Protocentral/Protocentral_ADS1220/src/Protocentral_ADS1220.h

//////////////////////////////////////////////////////////////////////////////////////////
//
//    Arduino library for the ADS1220 24-bit ADC breakout board
//
//    Author: Ashwin Whitchurch
//    Copyright (c) 2018 ProtoCentral
//
//    Based on original code from Texas Instruments
//
//    This software is licensed under the MIT License(http://opensource.org/licenses/MIT).
//
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
//   For information on how to use, visit https://github.com/Protocentral/Protocentral_ADS1220/
//
/////////////////////////////////////////////////////////////////////////////////////////

#pragma once

#include "Arduino.h"

#include <SPI.h>

//ADS1220 SPI commands
#define SPI_MASTER_DUMMY    0xFF
#define RESET               0x06   //Send the RESET command (06h) to make sure the ADS1220 is properly reset after power-up
#define START               0x08    //Send the START/SYNC command (08h) to start converting in continuous conversion mode
#define WREG  0x40
#define RREG  0x20

//Config registers
#define CONFIG_REG0_ADDRESS 0x00
#define CONFIG_REG1_ADDRESS 0x01
#define CONFIG_REG2_ADDRESS 0x02
#define CONFIG_REG3_ADDRESS 0x03

#define REG_CONFIG3_IDAC1routing_MASK    0xE0
#define REG_CONFIG3_IDAC2routing_MASK    0x1C
#define REG_CONFIG2_VREF_MASK            0xC0
#define REG_CONFIG2_FIR_MASK             0x30
#define REG_CONFIG2_IDACcurrent_MASK     0x07
#define REG_CONFIG1_MODE_MASK            0x18
#define REG_CONFIG1_DR_MASK       0xE0
#define REG_CONFIG0_PGA_GAIN_MASK 0x0E
#define REG_CONFIG0_MUX_MASK      0xF0

#define IDAC1_disable     0x00  
#define IDAC1_AIN0        0x20  
#define IDAC1_AIN1        0x40  
#define IDAC1_AIN2        0x60  
#define IDAC1_AIN3        0x80  
#define IDAC1_REFP0       0xA0  
#define IDAC1_REFN0       0xC0  
#define IDAC1_reserved    0xE0  

#define IDAC2_disable     0x00  
#define IDAC2_AIN0        0x04  
#define IDAC2_AIN1        0x08  
#define IDAC2_AIN2        0x0C  
#define IDAC2_AIN3        0x10  
#define IDAC2_REFP0       0x14  
#define IDAC2_REFN0       0x18  
#define IDAC2_reserved    0x1C  

#define IDAC_OFF     0x00  
#define IDAC_10      0x01  
#define IDAC_50      0x02  
#define IDAC_100     0x03  
#define IDAC_250     0x04  
#define IDAC_500     0x05  
#define IDAC_1000    0x06  
#define IDAC_1500    0x07  

#define FIR_OFF      0x00  
#define FIR_5060     0x10  
#define FIR_50Hz     0x20  
#define FIR_60Hz     0x30  

#define VREF_2048       0x00  
#define VREF_REFP0      0x40  
#define VREF_AIN0       0x80  
#define VREF_ANALOG     0xC0  

#define MODE_NORMAL     0x00  
#define MODE_DUTYCYCLE  0x08  
#define MODE_TURBO      0x10  
#define MODE_RESERVED   0x18  

#define DR_20SPS    0x00
#define DR_45SPS    0x20
#define DR_90SPS    0x40
#define DR_175SPS   0x60
#define DR_330SPS   0x80
#define DR_600SPS   0xA0
#define DR_1000SPS  0xC0

#define PGA_GAIN_1   0x00
#define PGA_GAIN_2   0x02
#define PGA_GAIN_4   0x04
#define PGA_GAIN_8   0x06
#define PGA_GAIN_16  0x08
#define PGA_GAIN_32  0x0A
#define PGA_GAIN_64  0x0C
#define PGA_GAIN_128 0x0E

#define MUX_AIN0_AIN1   0x00
#define MUX_AIN0_AIN2   0x10
#define MUX_AIN0_AIN3   0x20
#define MUX_AIN1_AIN2   0x30
#define MUX_AIN1_AIN3   0x40
#define MUX_AIN2_AIN3   0x50
#define MUX_AIN1_AIN0   0x60
#define MUX_AIN3_AIN2   0x70
#define MUX_AIN0_AVSS   0x80
#define MUX_AIN1_AVSS   0x90
#define MUX_AIN2_AVSS   0xA0
#define MUX_AIN3_AVSS   0xB0

#define MUX_SE_CH0      0x80
#define MUX_SE_CH1      0x90
#define MUX_SE_CH2      0xA0
#define MUX_SE_CH3      0xB0


class Protocentral_ADS1220
{
      private:
            uint8_t m_config_reg0;
            uint8_t m_config_reg1;
            uint8_t m_config_reg2;
            uint8_t m_config_reg3;

            uint8_t Config_Reg0;
            uint8_t Config_Reg1;
            uint8_t Config_Reg2;
            uint8_t Config_Reg3;

            uint8_t DataReg[3];

            uint8_t m_drdy_pin=6;
            uint8_t m_cs_pin=7;
      public:
            uint8_t NewDataAvailable;

            Protocentral_ADS1220();
            void begin(uint8_t cs_pin, uint8_t drdy_pin);

            void PrintRegisterValues();

            void Start_Conv(void);
            void ads1220_Reset(void);

            void SPI_Command(unsigned char data_in);
            void writeRegister(uint8_t address, uint8_t value);
            uint8_t readRegister(uint8_t address);
            uint8_t * Read_Data(void);
            int32_t Read_WaitForData();

            bool WaitForData(unsigned int timeout_ms);
            int32_t DataToInt();

            uint8_t * get_config_reg(void);

            // control register 0
            void select_mux_channels(int channels_conf);
            void set_pga_gain(int pgagain);
            void PGA_OFF(void);
            void PGA_ON(void);
            
            // control register 1
            void set_data_rate(int datarate);
            void set_OperationMode(int OPmode);    
            void set_conv_mode_single_shot(void);
            void set_conv_mode_continuous(void);
            void TemperatureSensorMode_enable(void);    
            void TemperatureSensorMode_disable(void);   
            void CurrentSources_ON(void);       
            void CurrentSources_OFF(void);      
            
            // control register 2
            void set_VREF(int vref);             
            void set_FIR_Filter(int filter);     
            void LowSideSwitch_OPEN(void);       
            void LowSideSwitch_CLOSED(void);        
            void set_IDAC_Current(int IDACcurrent);  
            
            // control register 3
            void set_IDAC1_Route(int IDAC1routing);   
            void set_IDAC2_Route(int IDAC2routing);   
            void DRDYmode_default(void);       
            void DRDYmode_DOUT(void);          
            
            // end control register
            int32_t Read_SingleShot_WaitForData(void);
            int32_t Read_SingleShot_SingleEnded_WaitForData(uint8_t channel_no);

            void internal_reference();
            void external_reference();

            int32_t Read_Data_Samples();
};
