Protocentral/Protocentral_ADS1220/examples/Example2-ADS1220-Stream/Example2-ADS1220-Stream.ino

//////////////////////////////////////////////////////////////////////////////////////////
//
//    Demo code for the ADS1220 24-bit ADC breakout board
//
//    Author: Ashwin Whitchurch
//    Copyright (c) 2018 ProtoCentral
//
//    This example gives differential voltage across the AN0 and AN1 pins in mVolts
//
//    Arduino connections:
//
//  |ADS1220 pin label| Pin Function         |Arduino Connection|
//  |-----------------|:--------------------:|-----------------:|
//  | DRDY            | Data ready Output pin|  D02             |
//  | MISO            | Slave Out            |  D12             |
//  | MOSI            | Slave In             |  D11             |
//  | SCLK            | Serial Clock         |  D13             |
//  | CS              | Chip Select          |  D7              |
//  | DVDD            | Digital VDD          |  +5V             |
//  | DGND            | Digital Gnd          |  Gnd             |
//  | AN0-AN3         | Analog Input         |  Analog Input    |
//  | AVDD            | Analog VDD           |  -               |
//  | AGND            | Analog Gnd           |  -               |
//
//    This software is licensed under the MIT License(http://opensource.org/licenses/MIT).
//
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
//   For information on how to use, visit https://github.com/Protocentral/Protocentral_ADS1220
//
/////////////////////////////////////////////////////////////////////////////////////////

#include "Protocentral_ADS1220.h"
#include <SPI.h>

#define PGA 32                // Programmable Gain, confirm that the same as set_pga_gain
#define VREF 2.048            // Internal reference of 2.048V
#define VFSR VREF/PGA
#define FSR (((long int)1<<23)-1)

#define ADS1220_CS_PIN    7
#define ADS1220_DRDY_PIN  2

Protocentral_ADS1220 pc_ads1220;
int32_t adc_data;
float ADS1220Temperature;
volatile bool drdyIntrFlag = false;

void drdyInterruptHndlr(){
  drdyIntrFlag = true;
}

void enableInterruptPin(){
  attachInterrupt(digitalPinToInterrupt(ADS1220_DRDY_PIN), drdyInterruptHndlr, FALLING);
}

void setup()
{
    Serial.begin(57600);

    pc_ads1220.begin(ADS1220_CS_PIN,ADS1220_DRDY_PIN);
    pc_ads1220.set_data_rate(DR_20SPS);
    pc_ads1220.set_pga_gain(PGA_GAIN_32);
    pc_ads1220.select_mux_channels(MUX_AIN0_AIN1);  //Configure for differential measurement between AIN0 and AIN1
    pc_ads1220.set_conv_mode_continuous();          //Set continuous conversion mode
    pc_ads1220.Start_Conv();  //Start continuous conversion mode

    enableInterruptPin();
}

void loop()
{
    if(drdyIntrFlag){
        drdyIntrFlag = false;

        adc_data=pc_ads1220.Read_Data_Samples();
        float Vout = (float)((adc_data*VFSR*1000)/FSR);     //In  mV
        readADS1220Temperature();  

        delay(300);

        Serial.print("Vout in mV : ");
        Serial.print(Vout);
        Serial.print("  32bit HEX : ");
        Serial.print(adc_data,HEX);
        Serial.print("  Temp in °C : ");
        Serial.println(ADS1220Temperature,5);      
    }
}

void readADS1220Temperature()
{
    pc_ads1220.TemperatureSensorMode_enable();
        delay(50);                                                              // waiting time after register changed, for 20SPS
    ADS1220Temperature = (pc_ads1220.Read_Data_Samples() / 1000 * 0.03125);     //In  °C
    pc_ads1220.TemperatureSensorMode_disable();
        delay(50);                                                              // waiting time after register changed, for 20SPS
}
